thejpster/monotron/avr_kb/src/keycodes.h

/**
 * Keycodes for Scan Code Set 2.
 */

#define KEYCODE_SCS2_F9 0x01
#define KEYCODE_SCS2_F5 0x03
#define KEYCODE_SCS2_F3 0x04
#define KEYCODE_SCS2_F1 0x05
#define KEYCODE_SCS2_F2 0x06
#define KEYCODE_SCS2_F12 0x07
#define KEYCODE_SCS2_F10 0x09
#define KEYCODE_SCS2_F8 0x0A
#define KEYCODE_SCS2_F6 0x0B
#define KEYCODE_SCS2_F4 0x0C
#define KEYCODE_SCS2_TAB 0x0D
#define KEYCODE_SCS2_BACKTICK 0x0E
#define KEYCODE_SCS2_ALTLEFT 0x11
#define KEYCODE_SCS2_SHIFTLEFT 0x12
#define KEYCODE_SCS2_CONTROLLEFT 0x14
#define KEYCODE_SCS2_Q 0x15
#define KEYCODE_SCS2_KEY1 0x16
#define KEYCODE_SCS2_Z 0x1A
#define KEYCODE_SCS2_S 0x1B
#define KEYCODE_SCS2_A 0x1C
#define KEYCODE_SCS2_W 0x1D
#define KEYCODE_SCS2_KEY2 0x1e
#define KEYCODE_SCS2_C 0x21
#define KEYCODE_SCS2_X 0x22
#define KEYCODE_SCS2_D 0x23
#define KEYCODE_SCS2_E 0x24
#define KEYCODE_SCS2_KEY4 0x25
#define KEYCODE_SCS2_KEY3 0x26
#define KEYCODE_SCS2_SPACEBAR 0x29
#define KEYCODE_SCS2_V 0x2A
#define KEYCODE_SCS2_F 0x2B
#define KEYCODE_SCS2_T 0x2C
#define KEYCODE_SCS2_R 0x2D
#define KEYCODE_SCS2_KEY5 0x2E
#define KEYCODE_SCS2_N 0x31
#define KEYCODE_SCS2_B 0x32
#define KEYCODE_SCS2_H 0x33
#define KEYCODE_SCS2_G 0x34
#define KEYCODE_SCS2_Y 0x35
#define KEYCODE_SCS2_KEY6 0x36
#define KEYCODE_SCS2_M 0x3A
#define KEYCODE_SCS2_J 0x3B
#define KEYCODE_SCS2_U 0x3C
#define KEYCODE_SCS2_KEY7 0x3D
#define KEYCODE_SCS2_KEY8 0x3E
#define KEYCODE_SCS2_COMMA 0x41
#define KEYCODE_SCS2_K 0x42
#define KEYCODE_SCS2_I 0x43
#define KEYCODE_SCS2_O 0x44
#define KEYCODE_SCS2_KEY0 0x45
#define KEYCODE_SCS2_KEY9 0x46
#define KEYCODE_SCS2_FULLSTOP 0x49
#define KEYCODE_SCS2_SLASH 0x4A
#define KEYCODE_SCS2_L 0x4B
#define KEYCODE_SCS2_SEMICOLON 0x4C
#define KEYCODE_SCS2_P 0x4D
#define KEYCODE_SCS2_MINUS 0x4E
#define KEYCODE_SCS2_QUOTE 0x52
#define KEYCODE_SCS2_BRACKETSQUARELEFT 0x54
#define KEYCODE_SCS2_EQUALS 0x55
#define KEYCODE_SCS2_CAPSLOCK 0x58
#define KEYCODE_SCS2_SHIFTRIGHT 0x59
#define KEYCODE_SCS2_ENTER 0x5A
#define KEYCODE_SCS2_BRACKETSQUARERIGHT 0x5B
#define KEYCODE_SCS2_BACKSLASH 0x5D
#define KEYCODE_SCS2_BACKSPACE 0x66
#define KEYCODE_SCS2_NUMPAD1 0x69
#define KEYCODE_SCS2_NUMPAD4 0x6B
#define KEYCODE_SCS2_NUMPAD7 0x6C
#define KEYCODE_SCS2_NUMPAD0 0x70
#define KEYCODE_SCS2_NUMPADPERIOD 0x71
#define KEYCODE_SCS2_NUMPAD2 0x72
#define KEYCODE_SCS2_NUMPAD5 0x73
#define KEYCODE_SCS2_NUMPAD6 0x74
#define KEYCODE_SCS2_NUMPAD8 0x75
#define KEYCODE_SCS2_ESCAPE 0x76
#define KEYCODE_SCS2_NUMPADLOCK 0x77
#define KEYCODE_SCS2_F11 0x78
#define KEYCODE_SCS2_NUMPADPLUS 0x79
#define KEYCODE_SCS2_NUMPAD3 0x7A
#define KEYCODE_SCS2_NUMPADMINUS 0x7B
#define KEYCODE_SCS2_NUMPADSTAR 0x7C
#define KEYCODE_SCS2_NUMPAD9 0x7D
#define KEYCODE_SCS2_SCROLLLOCK 0x7E
#define KEYCODE_SCS2_F7 0x83

#define KEYCODE_SCS2_EXTENDED_ALTRIGHT 0x11
#define KEYCODE_SCS2_EXTENDED_CONTROLRIGHT 0x14
#define KEYCODE_SCS2_EXTENDED_WINDOWSLEFT 0x1F
#define KEYCODE_SCS2_EXTENDED_WINDOWSRIGHT 0x27
#define KEYCODE_SCS2_EXTENDED_MENUS 0x2F
#define KEYCODE_SCS2_EXTENDED_NUMPADSLASH 0x4A
#define KEYCODE_SCS2_EXTENDED_NUMPADENTER 0x5A
#define KEYCODE_SCS2_EXTENDED_END 0x69
#define KEYCODE_SCS2_EXTENDED_ARROWLEFT 0x6B
#define KEYCODE_SCS2_EXTENDED_HOME 0x6C
#define KEYCODE_SCS2_EXTENDED_INSERT 0x70
#define KEYCODE_SCS2_EXTENDED_DELETE 0x71
#define KEYCODE_SCS2_EXTENDED_ARROWDOWN 0x72
#define KEYCODE_SCS2_EXTENDED_ARROWRIGHT 0x74
#define KEYCODE_SCS2_EXTENDED_ARROWUP 0x75
#define KEYCODE_SCS2_EXTENDED_PAGEDOWN 0x7A
#define KEYCODE_SCS2_EXTENDED_PAGEUP 0x7D
