thejpster/monotron/src/ui/mod.rs

use super::{Context, Input, APPLICATION_RAM, FRAMEBUFFER};
use asm;
use core::fmt::Write;
use embedded_hal::prelude::*;
use fb;
use fb::{BaseConsole, AsciiConsole};
use menu;

mod rust_logo;

pub(crate) type Menu<'a> = menu::Menu<'a, Context>;
pub(crate) type Item<'a> = menu::Item<'a, Context>;

const TEST_ALPHABET: Item = Item {
    item_type: menu::ItemType::Callback(test_alphabet),
    command: "alphabet",
    help: Some("Scrolls some test text output."),
};

const TEST_CLEAR: Item = Item {
    item_type: menu::ItemType::Callback(test_clear),
    command: "clear",
    help: Some("Resets the display."),
};

const TEST_ANIMATION: Item = Item {
    item_type: menu::ItemType::Callback(test_animation),
    command: "animate",
    help: Some("Bounces argument around."),
};

const TEST_ART: Item = Item {
    item_type: menu::ItemType::Callback(test_art),
    command: "art",
    help: Some("Show some art."),
};

const ITEM_PEEK: Item = Item {
    item_type: menu::ItemType::Callback(item_peek),
    command: "peek",
    help: Some("<addr> - Read a register."),
};

const ITEM_POKE: Item = Item {
    item_type: menu::ItemType::Callback(item_poke),
    command: "poke",
    help: Some("<addr> <value> - Write a register."),
};

const ITEM_DUMP: Item = Item {
    item_type: menu::ItemType::Callback(item_dump),
    command: "dump",
    help: Some("<addr> <bytes> - Dump RAM/ROM."),
};

const ITEM_LOAD: Item = Item {
    item_type: menu::ItemType::Callback(load_file),
    command: "load",
    help: Some("<len> - Load program from UART."),
};

const ITEM_DEBUG: Item = Item {
    item_type: menu::ItemType::Callback(debug_info),
    command: "debug",
    help: Some("- Show some debug info."),
};

const ITEM_RUN: Item = Item {
    item_type: menu::ItemType::Callback(run_program),
    command: "run",
    help: Some("Run loaded program."),
};

pub(crate) const ROOT_MENU: Menu = Menu {
    label: "root",
    items: &[
        &TEST_ALPHABET,
        &TEST_ANIMATION,
        &TEST_ART,
        &TEST_CLEAR,
        &ITEM_PEEK,
        &ITEM_POKE,
        &ITEM_DUMP,
        &ITEM_LOAD,
        &ITEM_RUN,
        &ITEM_DEBUG,
    ],
    entry: None,
    exit: None,
};

struct Fire {
    seed: u32,
    buffer: [u32; Fire::FLAME_BUFFER_LEN],
}

/// The test menu item - displays all the glyphs in all the colour combinations
fn test_alphabet<'a>(_menu: &Menu, _item: &Item, _input: &str, context: &mut Context) {
    let mut old_frame = 0;
    let mut ch = 0u8;
    const COLOURS: [fb::Colour; 8] = [
        fb::Colour::Blue,
        fb::Colour::Black,
        fb::Colour::Red,
        fb::Colour::Magenta,
        fb::Colour::Green,
        fb::Colour::Yellow,
        fb::Colour::Cyan,
        fb::Colour::White,
    ];
    let mut fg_wheel = COLOURS.iter().cycle();
    let mut bg_wheel = COLOURS.iter().cycle();
    let mut fg = fg_wheel.next();
    let mut bg = bg_wheel.next();
    loop {
        asm::wfi();
        let new_frame = unsafe { FRAMEBUFFER.frame() };
        if new_frame != old_frame {
            old_frame = new_frame;
            unsafe {
                FRAMEBUFFER.write_glyph(
                    fb::Char::from_byte(ch),
                    Some(fb::Attr::new(*fg.unwrap(), *bg.unwrap())),
                );
            }
            fg = fg_wheel.next();
            if ch == 255 {
                bg = bg_wheel.next();
                ch = 0;
            } else {
                ch += 1;
            }
        }
        if let Some(_input) = context.read() {
            break;
        }
    }
}

/// Clears the screen
fn test_clear<'a>(_menu: &Menu, _item: &Item, _input: &str, _context: &mut Context) {
    unsafe { FRAMEBUFFER.clear() };
    unsafe { FRAMEBUFFER.set_pos(fb::Position::origin()).unwrap() };
}

/// Display some art
fn test_art<'a>(_menu: &Menu, _item: &Item, _input: &str, context: &mut Context) {
    unsafe {
        FRAMEBUFFER.clear();
    }
    write!(context, "SCORE 0300      HIGH 0000          3    ╩       ").unwrap();
    write!(context, "  ▀▄ ▄▀     ▀▄ ▄▀     ▀▄ ▄▀     ▀▄ ▄▀           ").unwrap();
    write!(context, " ▄█▀█▀█▄   ▄█▀█▀█▄   ▄█▀█▀█▄   ▄█▀█▀█▄          ").unwrap();
    write!(context, "█▀█████▀█ █▀█████▀█ █▀█████▀█ █▀█████▀█         ").unwrap();
    write!(context, "▀ ▀▄ ▄▀ ▀ ▀ ▀▄ ▄▀ ▀ ▀ ▀▄ ▄▀ ▀ ▀ ▀▄ ▄▀ ▀         ").unwrap();
    writeln!(context, "").unwrap();
    write!(context, "  ▀▄ ▄▀     ▀▄ ▄▀     ▀▄ ▄▀     ▀▄ ▄▀           ").unwrap();
    write!(context, " ▄█▀█▀█▄   ▄█▀█▀█▄   ▄█▀█▀█▄   ▄█▀█▀█▄          ").unwrap();
    write!(context, "█▀█████▀█ █▀█████▀█ █▀█████▀█ █▀█████▀█         ").unwrap();
    write!(context, "▀ ▀▄ ▄▀ ▀ ▀ ▀▄ ▄▀ ▀ ▀ ▀▄ ▄▀ ▀ ▀ ▀▄ ▄▀ ▀         ").unwrap();
    writeln!(context, "").unwrap();
    write!(context, "  ▀▄ ▄▀     ▀▄ ▄▀     ▀▄ ▄▀     ▀▄ ▄▀           ").unwrap();
    write!(context, " ▄█▀█▀█▄   ▄█▀█▀█▄   ▄█▀█▀█▄   ▄█▀█▀█▄          ").unwrap();
    write!(context, "█▀█████▀█ █▀█████▀█ █▀█████▀█ █▀█████▀█         ").unwrap();
    write!(context, "▀ ▀▄ ▄▀ ▀ ▀ ▀▄ ▄▀ ▀ ▀ ▀▄ ▄▀ ▀ ▀ ▀▄ ▄▀ ▀         ").unwrap();
    writeln!(context, "").unwrap();
    writeln!(context, "        |").unwrap();
    write!(context, "  ██░▒  |   ████      ████      ████      ████  ").unwrap();
    write!(context, "██████▓▓  ████████  ████████  ████████  ████████").unwrap();
    writeln!(context, "").unwrap();
    writeln!(context, "       ═╩═").unwrap();
    writeln!(context, "Press a key...").unwrap();
    loop {
        asm::wfi();
        if let Some(_input) = context.read() {
            break;
        }
    }
    writeln!(context, "\u{001b}Y\u{001b}k\u{001b}Z").unwrap();
    writeln!(context, "              1UP   HIGH SCORE").unwrap();
    writeln!(context, "                00        00").unwrap();
    writeln!(context, "\u{001b}G          ╔════════════╦╦════════════╗").unwrap();
    writeln!(context, "          ║\u{001b}C············\u{001b}G║║\u{001b}C············\u{001b}G║").unwrap();
    writeln!(context, "          ║\u{001b}C·\u{001b}G┌──┐\u{001b}C·\u{001b}G┌───┐\u{001b}C·\u{001b}G║║\u{001b}C·\u{001b}G┌───┐\u{001b}C·\u{001b}G┌──┐\u{001b}C·\u{001b}G║").unwrap();
    writeln!(context, "          ║○│  │\u{001b}C·\u{001b}G│   │\u{001b}C·\u{001b}G║║\u{001b}C·\u{001b}G│   │\u{001b}C·\u{001b}G│  │○║").unwrap();
    writeln!(context, "          ║\u{001b}C·\u{001b}G└──┘\u{001b}C·\u{001b}G└───┘\u{001b}C·\u{001b}G╚╝\u{001b}C·\u{001b}G└───┘\u{001b}C·\u{001b}G└──┘\u{001b}C·\u{001b}G║").unwrap();
    writeln!(context, "          ║\u{001b}C··························\u{001b}G║").unwrap();
    writeln!(context, "          ║\u{001b}C·\u{001b}G┌──┐\u{001b}C·\u{001b}G┌┐\u{001b}C·\u{001b}G┌──────┐\u{001b}C·\u{001b}G┌┐\u{001b}C·\u{001b}G┌──┐\u{001b}C·\u{001b}G║").unwrap();
    writeln!(context, "          ║\u{001b}C·\u{001b}G└──┘\u{001b}C·\u{001b}G││\u{001b}C·\u{001b}G└──┐┌──┘\u{001b}C·\u{001b}G││\u{001b}C·\u{001b}G└──┘\u{001b}C·\u{001b}G║").unwrap();
    writeln!(context, "          ║\u{001b}C······\u{001b}G││\u{001b}C····\u{001b}G││\u{001b}C····\u{001b}G││\u{001b}C······\u{001b}G║").unwrap();
    writeln!(context, "          ╚════╗\u{001b}C·\u{001b}G│└──┐ ││ ┌──┘│\u{001b}C·\u{001b}G╔════╝").unwrap();
    writeln!(context, "               ║\u{001b}C·\u{001b}G│┌──┘ └┘ └──┐│\u{001b}C·\u{001b}G║     ").unwrap();
    writeln!(context, "               ║\u{001b}C·\u{001b}G││    \u{001b}Y☺\u{001b}G     ││\u{001b}C·\u{001b}G║     ").unwrap();
    writeln!(context, "          ═════╝\u{001b}C·\u{001b}G└┘ ╔══════╗ └┘\u{001b}C·\u{001b}G╚═════").unwrap();
    writeln!(context, "                \u{001b}C·\u{001b}G   ║\u{001b}R☺ \u{001b}G☺ \u{001b}B☺\u{001b}G ║   \u{001b}C·\u{001b}G      ").unwrap();
    writeln!(context, "          ═════╗\u{001b}C·\u{001b}G┌┐ ╚══════╝ ┌┐\u{001b}C·\u{001b}G╔═════").unwrap();
    writeln!(context, "               ║\u{001b}C·\u{001b}G││  READY!  ││\u{001b}C·\u{001b}G║     ").unwrap();
    writeln!(context, "               ║\u{001b}C·\u{001b}G││ ┌──────┐ ││\u{001b}C·\u{001b}G║     ").unwrap();
    writeln!(context, "          ╔════╝\u{001b}C·\u{001b}G└┘ └──┐┌──┘ └┘\u{001b}C·\u{001b}G╚════╗").unwrap();
    writeln!(context, "          ║\u{001b}C············\u{001b}G││\u{001b}C············\u{001b}G║").unwrap();
    writeln!(context, "          ║\u{001b}C·\u{001b}G┌──┐\u{001b}C·\u{001b}G┌───┐\u{001b}C·\u{001b}G││\u{001b}C·\u{001b}G┌───┐\u{001b}C·\u{001b}G┌──┐\u{001b}C·\u{001b}G║").unwrap();
    writeln!(context, "          ║\u{001b}C·\u{001b}G└─┐│\u{001b}C·\u{001b}G└───┘\u{001b}C·\u{001b}G└┘\u{001b}C·\u{001b}G└───┘\u{001b}C·\u{001b}G│┌─┘\u{001b}C·\u{001b}G║").unwrap();
    writeln!(context, "          ║○\u{001b}C··\u{001b}G││\u{001b}C·······\u{001b}Y◄►\u{001b}C·······\u{001b}G││\u{001b}C··\u{001b}G○║").unwrap();
    writeln!(context, "          ╠═╗\u{001b}C·\u{001b}G││\u{001b}C·\u{001b}G┌┐\u{001b}C·\u{001b}G┌──────┐\u{001b}C·\u{001b}G┌┐\u{001b}C·\u{001b}G││\u{001b}C·\u{001b}G╔═╣").unwrap();
    writeln!(context, "          ╠═╝\u{001b}C·\u{001b}G└┘\u{001b}C·\u{001b}G││\u{001b}C·\u{001b}G└──┐┌──┘\u{001b}C·\u{001b}G││\u{001b}C·\u{001b}G└┘\u{001b}C·\u{001b}G╚═╣").unwrap();
    writeln!(context, "          ║\u{001b}C······\u{001b}G││\u{001b}C····\u{001b}G││\u{001b}C····\u{001b}G││\u{001b}C······\u{001b}G║").unwrap();
    writeln!(context, "          ║\u{001b}C·\u{001b}G┌────┘└──┐\u{001b}C·\u{001b}G││\u{001b}C·\u{001b}G┌──┘└────┐\u{001b}C·\u{001b}G║").unwrap();
    writeln!(context, "          ║\u{001b}C·\u{001b}G└────────┘\u{001b}C·\u{001b}G└┘\u{001b}C·\u{001b}G└────────┘\u{001b}C·\u{001b}G║").unwrap();
    writeln!(context, "          ║\u{001b}C··························\u{001b}G║").unwrap();
    writeln!(context, "          ╚══════════════════════════╝").unwrap();
    writeln!(context, "             ◄► ◄► ◄►").unwrap();
    write!(context, "\n\n\nPress a key...").unwrap();
    loop {
        asm::wfi();
        if let Some(_input) = context.read() {
            break;
        }
    }

    write!(context, "\u{001b}Z\u{001b}K\u{001b}w  \u{001b}RF\u{001b}Kile   \u{001b}RE\u{001b}Kdit  \u{001b}RV\u{001b}Kiew   \u{001b}RT\u{001b}Kools  \u{001b}RH\u{001b}Kelp               ").unwrap();
    write!(context, "\u{001b}B\u{001b}c████████████████████████████████████████████████").unwrap();
    write!(context, "████████████████████████████████████████████████").unwrap();
    write!(context, "████████████████████████████████████████████████").unwrap();
    write!(context, "████████████████████████████████████████████████").unwrap();
    write!(context, "████████████████████████████████████████████████").unwrap();
    write!(context, "████████████████████████████████████████████████").unwrap();
    write!(context, "████████████████████████████████████████████████").unwrap();
    write!(context, "████████████████████████████\u{001b}W\u{001b}b┌[Calc]──X┐    \u{001b}B\u{001b}c█████").unwrap();
    write!(context, "████████████████████████████\u{001b}W\u{001b}b│\u{001b}B\u{001b}k         \u{001b}W\u{001b}b│\u{001b}B\u{001b}k▒\u{001b}c██\u{001b}W\u{001b}b \u{001b}B\u{001b}c█████").unwrap();
    write!(context, "███\u{001b}W\u{001b}m┌[Calendar]───────────X┐\u{001b}B\u{001b}c█\u{001b}W\u{001b}b│\u{001b}B\u{001b}k         \u{001b}W\u{001b}b│\u{001b}B\u{001b}k▒\u{001b}c██\u{001b}W\u{001b}b \u{001b}B\u{001b}c█████").unwrap();
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
    write!(context, "███\u{001b}W\u{001b}m└──────────────────────┘\u{001b}B\u{001b}k▒\u{001b}c████████████████████").unwrap();
    write!(context, "████\u{001b}k▒▒▒▒▒▒▒▒▒▒▒▒▒▒▒▒▒▒▒▒▒▒▒▒\u{001b}c████████████████████").unwrap();
    write!(context, "████████████████████████████████████████████████").unwrap();
    write!(context, "████████████████████████████████████████████████").unwrap();
    write!(context, "████████████████████████████████████████████████").unwrap();
    write!(context, "████████████████████████████████████████████████").unwrap();
    write!(context, "████████████████████████████████████████████████").unwrap();
    write!(context, "████████████████████████████████████████████████").unwrap();
    write!(context, "\u{001b}K\u{001b}w▒\u{001b}W\u{001b}kCAPS\u{001b}K\u{001b}w▒\u{001b}W\u{001b}kINS\u{001b}K\u{001b}w▒▒▒▒▒▒▒▒▒▒▒▒▒▒▒▒▒▒▒▒▒▒▒▒\u{001b}W\u{001b}k[Version v1.2]\u{001b}K\u{001b}w").unwrap();

    loop {
        asm::wfi();
        if let Some(_input) = context.read() {
            writeln!(context, "\u{001b}W\u{001b}b\u{001b}ZOk...").unwrap();
            break;
        }
    }

    write!(context, "\u{001b}Z\u{001b}Y\u{001b}k╔════════════════════════\u{001b}W[MonotronPaint]\u{001b}Y═══════╗").unwrap();
    write!(context, "║\u{001b}W┌[Font]──────────┐┌──────────────────────────┐\u{001b}Y║").unwrap();
    write!(context, "║\u{001b}W│ ☺☻♥♦♣♠•◘○◙♂♀♪♫☼││\u{001b}Y\u{001b}b                          \u{001b}W\u{001b}k│\u{001b}Y║").unwrap();
    write!(context, "║\u{001b}W│►◄↕‼¶§▬↨↑↓→←∟↔▲▼││\u{001b}Y\u{001b}b                          \u{001b}W\u{001b}k│\u{001b}Y║").unwrap();
    write!(context, "║\u{001b}W│ !\"#$%&'()*+,-./││\u{001b}Y\u{001b}b                          \u{001b}W\u{001b}k│\u{001b}Y║").unwrap();
    write!(context, "║\u{001b}W│0123456789:;<=>?││\u{001b}Y\u{001b}b                          \u{001b}W\u{001b}k│\u{001b}Y║").unwrap();
    write!(context, "║\u{001b}W│@ABCDEFGHIJKLMNO││\u{001b}Y\u{001b}b                          \u{001b}W\u{001b}k│\u{001b}Y║").unwrap();
    write!(context, "║\u{001b}W│PQRSTUVWXYZ[\\]^_││\u{001b}Y\u{001b}b          ▓▓▓▓▓▓▓         \u{001b}W\u{001b}k│\u{001b}Y║").unwrap();
    write!(context, "║\u{001b}W│`abcdefghijklmno││\u{001b}Y\u{001b}b        ▓▓▓▓▓▓▓▓▓▓▓       \u{001b}W\u{001b}k│\u{001b}Y║").unwrap();
    write!(context, "║\u{001b}W│pqrstuvwxyz{{|}}~ ││\u{001b}Y\u{001b}b       ▓▓▓▓▓▓▓▓▓▓▓▓▓      \u{001b}W\u{001b}k│\u{001b}Y║").unwrap();
    write!(context, "║\u{001b}W│ÇüéâäàåçêëèïîìÄÅ││\u{001b}Y\u{001b}b     ▓▓▓▓▓▓▓▓▓▓▓▓▓▓▓▓▓    \u{001b}W\u{001b}k│\u{001b}Y║").unwrap();
    write!(context, "║\u{001b}W│ÉæÆôöòûùÿÖÜø£Ø×ƒ││\u{001b}Y\u{001b}b     ▓▓▓▓▓▓▓▓▓▓▓▓▓▓▓▓▓    \u{001b}W\u{001b}k│\u{001b}Y║").unwrap();
    write!(context, "║\u{001b}W│áíóúñÑªº¿®¬½¼¡«»││\u{001b}Y\u{001b}b    ▓▓▓\u{001b}K\u{001b}k▓▓▓\u{001b}Y\u{001b}b▓▓▓▓▓▓\u{001b}K\u{001b}k▓▓▓\u{001b}Y\u{001b}b▓▓▓▓   \u{001b}W\u{001b}k│\u{001b}Y║").unwrap();
    write!(context, "║\u{001b}W│░▒▓│┤ÁÂÀ©╣║╗╝¢¥┐││\u{001b}Y\u{001b}b   ▓▓▓\u{001b}K\u{001b}k▓▓▓▓▓\u{001b}Y\u{001b}b▓▓▓▓\u{001b}K\u{001b}k▓▓▓▓▓\u{001b}Y\u{001b}b▓▓▓▓  \u{001b}W\u{001b}k│\u{001b}Y║").unwrap();
    write!(context, "║\u{001b}W│└┴┬├─┼ãÃ╚╔╩╦╠═╬¤││\u{001b}Y\u{001b}b   ▓▓▓\u{001b}K\u{001b}k▓▓▓▓▓\u{001b}Y\u{001b}b▓▓▓▓\u{001b}K\u{001b}k▓▓▓▓▓\u{001b}Y\u{001b}b▓▓▓▓  \u{001b}W\u{001b}k│\u{001b}Y║").unwrap();
    write!(context, "║\u{001b}W│ðÐÊËÈıÍÎÏ┘┌█▄¦Ì▀││\u{001b}Y\u{001b}b  ▓▓▓▓\u{001b}K\u{001b}k▓▓▓▓▓\u{001b}Y\u{001b}b▓▓▓▓\u{001b}K\u{001b}k▓▓▓▓▓\u{001b}Y\u{001b}b▓▓▓▓▓ \u{001b}W\u{001b}k│\u{001b}Y║").unwrap();
    write!(context, "║\u{001b}W│ÓßÔÒõÕµþÞÚÛÙýÝ¯´││\u{001b}Y\u{001b}b  ▓▓▓▓▓\u{001b}K\u{001b}k▓▓▓\u{001b}Y\u{001b}b▓▓▓▓▓▓\u{001b}K\u{001b}k▓▓▓\u{001b}Y\u{001b}b▓▓▓▓▓▓ \u{001b}W\u{001b}k│\u{001b}Y║").unwrap();
    write!(context, "║\u{001b}W│-±‗¾¶§÷¸°¨·¹³²■\u{00a0}││\u{001b}Y\u{001b}b  ▓▓▓▓▓▓▓▓▓▓▓▓▓▓▓▓▓▓▓▓▓▓▓ \u{001b}W\u{001b}k│\u{001b}Y║").unwrap();
    write!(context, "║\u{001b}W└────────────────┘│\u{001b}Y\u{001b}b  ▓▓▓▓▓▓▓▓▓▓▓▓▓▓▓▓▓▓▓▓▓▓▓ \u{001b}W\u{001b}k│\u{001b}Y║").unwrap();
    write!(context, "║\u{001b}W┌[Colour]┐┌[Menu]┐│\u{001b}Y\u{001b}b  ▓▓▓▓▓▓▓▓▓▓▓▓▓▓▓▓▓▓▓▓▓▓▓ \u{001b}W\u{001b}k│\u{001b}Y║").unwrap();
    write!(context, "║\u{001b}W│\u{001b}R█\u{001b}G█\u{001b}B█\u{001b}Y█\u{001b}M█\u{001b}C█\u{001b}K█\u{001b}W█││L\u{001b}Mo\u{001b}Wad\u{001b}K  \u{001b}W││\u{001b}Y\u{001b}b  ▓▓▓▓▓\u{001b}K\u{001b}k▓\u{001b}Y\u{001b}b▓▓▓▓▓▓▓▓▓▓▓▓\u{001b}K\u{001b}k▓\u{001b}Y\u{001b}b▓▓▓▓ \u{001b}W\u{001b}k│\u{001b}Y║").unwrap();
    write!(context, "║\u{001b}W└────────┘│\u{001b}MS\u{001b}Wave\u{001b}K  \u{001b}W││\u{001b}Y\u{001b}b  ▓▓▓▓▓\u{001b}K\u{001b}k▓▓\u{001b}Y\u{001b}b▓▓▓▓▓▓▓▓▓▓\u{001b}K\u{001b}k▓▓\u{001b}Y\u{001b}b▓▓▓▓ \u{001b}W\u{001b}k│\u{001b}Y║").unwrap();
    write!(context, "║\u{001b}W┌[Tools]─┐│\u{001b}MP\u{001b}Wrint\u{001b}K \u{001b}W││\u{001b}Y\u{001b}b   ▓▓▓▓▓\u{001b}K\u{001b}k▓▓\u{001b}Y\u{001b}b▓▓▓▓▓▓▓▓▓\u{001b}K\u{001b}k▓\u{001b}Y\u{001b}b▓▓▓▓  \u{001b}W\u{001b}k│\u{001b}Y║").unwrap();
    write!(context, "║\u{001b}W│\u{001b}MR\u{001b}Wect\u{001b}K    \u{001b}W││\u{001b}ME\u{001b}Wxport││\u{001b}Y\u{001b}b   ▓▓▓▓▓▓\u{001b}K\u{001b}k▓\u{001b}Y\u{001b}b▓▓▓▓▓▓▓\u{001b}K\u{001b}k▓▓▓\u{001b}Y\u{001b}b▓▓▓▓  \u{001b}W\u{001b}k│\u{001b}Y║").unwrap();
    write!(context, "║\u{001b}W│\u{001b}MC\u{001b}Well\u{001b}K    \u{001b}W││C\u{001b}Ml\u{001b}Wear\u{001b}K \u{001b}W││\u{001b}Y\u{001b}b    ▓▓▓▓▓▓\u{001b}K\u{001b}k▓▓▓▓▓▓▓▓\u{001b}Y\u{001b}b▓▓▓▓▓   \u{001b}W\u{001b}k│\u{001b}Y║").unwrap();
    write!(context, "║\u{001b}W│\u{001b}ML\u{001b}Wine\u{001b}K    \u{001b}W││\u{001b}K      \u{001b}W││\u{001b}Y\u{001b}b     ▓▓▓▓▓▓▓▓▓▓▓▓▓▓▓▓▓    \u{001b}W\u{001b}k│\u{001b}Y║").unwrap();
    write!(context, "║\u{001b}W│\u{001b}MF\u{001b}Will\u{001b}K    \u{001b}W│└──────┘│\u{001b}Y\u{001b}b     ▓▓▓▓▓▓▓▓▓▓▓▓▓▓▓▓▓    \u{001b}W\u{001b}k│\u{001b}Y║").unwrap();
    write!(context, "║\u{001b}W│\u{001b}M\u{001b}cT\u{001b}Kext    \u{001b}W\u{001b}k│┌[Layr]┐│\u{001b}Y\u{001b}b       ▓▓▓▓▓▓▓▓▓▓▓▓▓      \u{001b}W\u{001b}k│\u{001b}Y║").unwrap();
    write!(context, "║\u{001b}W│\u{001b}MC\u{001b}Wopy\u{001b}K    \u{001b}W││\u{001b}K      \u{001b}W││\u{001b}Y\u{001b}b        ▓▓▓▓▓▓▓▓▓▓▓       \u{001b}W\u{001b}k│\u{001b}Y║").unwrap();
    write!(context, "║\u{001b}W│\u{001b}MP\u{001b}Waste\u{001b}K   \u{001b}W││1  \u{001b}GH\u{001b}RL\u{001b}WX││\u{001b}Y\u{001b}b          ▓▓▓▓▓▓▓         \u{001b}W\u{001b}k│\u{001b}Y║").unwrap();
    write!(context, "║\u{001b}W└────────┘│2  \u{001b}GH\u{001b}RL\u{001b}WX││\u{001b}Y\u{001b}b                          \u{001b}W\u{001b}k│\u{001b}Y║").unwrap();
    write!(context, "║\u{001b}W┌[Info]──┐│3  \u{001b}RH\u{001b}GL\u{001b}WX││\u{001b}Y\u{001b}b                          \u{001b}W\u{001b}k│\u{001b}Y║").unwrap();
    write!(context, "║\u{001b}W│N:Test\u{001b}K  \u{001b}W││4  \u{001b}GHL\u{001b}WX││\u{001b}Y\u{001b}b                          \u{001b}W\u{001b}k│\u{001b}Y║").unwrap();
    write!(context, "║\u{001b}W│S:48x36 ││\u{001b}K      \u{001b}W││\u{001b}Y\u{001b}b                          \u{001b}W\u{001b}k│\u{001b}Y║").unwrap();
    write!(context, "║\u{001b}W└────────┘└──────┘└──────────────────────────┘\u{001b}Y║").unwrap();
    write!(context, "╚══════════════════════════════════════════════").unwrap();

    loop {
        asm::wfi();
        if let Some(_input) = context.read() {
            break;
        }
    }

    let mode2_buffer = unsafe { &mut super::APPLICATION_RAM[0..384 * 288 / 8] };

    unsafe {
        FRAMEBUFFER.clear();
    }

    for (src, dest) in rust_logo::RUST_LOGO_DATA
        .iter()
        .zip(mode2_buffer.iter_mut())
    {
        // Our source is an X-Bitmap, which puts the pixels in LSB-first order.
        // We need MSB first order for Monotron.
        *dest = flip_byte(*src);
    }

    // Attach a graphical buffer at a scan-line. It is interpreted as
    // being a grid 48 bytes wide and as long as given. Each line
    // is output twice. We've attached it to the first scan-line.
    unsafe {
        FRAMEBUFFER.mode2(mode2_buffer, 0);
    }
    let mut start = 0;
    let mut up = true;

    let mut next_frame = unsafe { FRAMEBUFFER.frame() } + 1;
    loop {
        asm::wfi();
        let this_frame = unsafe { FRAMEBUFFER.frame() };
        if this_frame == next_frame {
            if up {
                start += 1;
                if start == 288 {
                    up = false;
                }
            } else {
                start -= 1;
                if start == 0 {
                    up = true;
                }
            }
            unsafe {
                FRAMEBUFFER.mode2_shift(start);
            }
            next_frame = this_frame + 1;
        }
        if let Some(_input) = context.read() {
            break;
        }
    }

    unsafe {
        FRAMEBUFFER.mode2_release();
    }

    write!(context, "\u{001b}Z\u{001b}W\u{001b}k╔══════════════════════════════════════════════╗").unwrap();
    write!(context, "║\u{001b}R█████\u{001b}K \u{001b}R\u{001b}y█████\u{001b}K\u{001b}k \u{001b}Y██  █\u{001b}K \u{001b}G█████\u{001b}K \u{001b}G\u{001b}y█\u{001b}k█\u{001b}y█\u{001b}k██\u{001b}K \u{001b}B████\u{001b}K \u{001b}B█████\u{001b}K \u{001b}M██  █\u{001b}W║").unwrap();
    write!(context, "║\u{001b}R▓\u{001b}K \u{001b}R▓\u{001b}K \u{001b}R▓\u{001b}K \u{001b}R\u{001b}y▓\u{001b}K\u{001b}k   \u{001b}R\u{001b}y▓\u{001b}K\u{001b}k \u{001b}Y▓\u{001b}K \u{001b}Y▓ ▓\u{001b}K \u{001b}G▓\u{001b}K   \u{001b}G▓\u{001b}K \u{001b}G \u{001b}K \u{001b}G\u{001b}y▓\u{001b}K\u{001b}k \u{001b}G \u{001b}K \u{001b}B\u{001b}g▓\u{001b}K\u{001b}k  \u{001b}B\u{001b}g▓\u{001b}K\u{001b}k \u{001b}B▓\u{001b}K   \u{001b}B▓\u{001b}K \u{001b}M▓\u{001b}K \u{001b}M▓ ▓\u{001b}W║").unwrap();
    write!(context, "║\u{001b}R▒\u{001b}K \u{001b}R▒\u{001b}K \u{001b}R▒\u{001b}K \u{001b}R\u{001b}y▒\u{001b}K\u{001b}k   \u{001b}R\u{001b}y▒\u{001b}K\u{001b}k \u{001b}Y▒\u{001b}K  \u{001b}Y▒▒\u{001b}K \u{001b}G▒\u{001b}K   \u{001b}G▒\u{001b}K \u{001b}G \u{001b}K \u{001b}G\u{001b}y▒\u{001b}K\u{001b}k \u{001b}G \u{001b}K \u{001b}B\u{001b}g▒\u{001b}K\u{001b}k \u{001b}B\u{001b}g▒\u{001b}k \u{001b}K \u{001b}B▒\u{001b}K   \u{001b}B▒\u{001b}K \u{001b}M▒\u{001b}K \u{001b}M ▒▒\u{001b}W║").unwrap();
    write!(context, "║\u{001b}R░ ░\u{001b}K \u{001b}R░\u{001b}K \u{001b}R\u{001b}y░░░░░\u{001b}K\u{001b}k \u{001b}Y░   ░\u{001b}K \u{001b}G░░░░░\u{001b}K \u{001b}G  \u{001b}y░\u{001b}k  \u{001b}K \u{001b}B\u{001b}g░\u{001b}k  \u{001b}g░\u{001b}K\u{001b}k \u{001b}B░░░░░\u{001b}K \u{001b}M░   ░\u{001b}W║").unwrap();
    write!(context, "╚══════════════════════════════════════════════╝").unwrap();
    write!(context, "          by theJPster / @therealjpster").unwrap();
    let mut pos = fb::Position::new(fb::Row(6), fb::Col(0));
    let mut next_frame = unsafe { FRAMEBUFFER.frame() } + 1;
    let mut f = Fire::new();
    loop {
        asm::wfi();
        let this_frame = unsafe { FRAMEBUFFER.frame() };
        if this_frame == next_frame {
            next_frame = this_frame + 1;
            f.draw_fire(unsafe { &mut FRAMEBUFFER });
        }
        match unsafe { FRAMEBUFFER.line() } {
            Some(95) => {
                for col in 13..=21 {
                    pos.col = fb::Col(col);
                    unsafe {
                        FRAMEBUFFER
                            .set_attr_at(pos, fb::Attr::new(fb::Colour::Blue, fb::Colour::Black));
                    }
                }
            }
            Some(101) => {
                for col in 13..=21 {
                    pos.col = fb::Col(col);
                    unsafe {
                        FRAMEBUFFER
                            .set_attr_at(pos, fb::Attr::new(fb::Colour::White, fb::Colour::Black));
                    }
                }
            }
            Some(104) => {
                for col in 13..=21 {
                    pos.col = fb::Col(col);
                    unsafe {
                        FRAMEBUFFER
                            .set_attr_at(pos, fb::Attr::new(fb::Colour::Red, fb::Colour::Black));
                    }
                }
            }
            _ => {}
        }
        if let Some(_input) = context.read() {
            writeln!(context, "\u{001b}W\u{001b}k\u{001b}ZOk...").unwrap();
            break;
        }
    }
}

impl Fire {
    const WIDTH: usize = 48;
    const HEIGHT: usize = 20;
    const SIZE: usize = Self::WIDTH * Self::HEIGHT;
    const FLAME_BUFFER_LEN: usize = Self::SIZE + Self::WIDTH + 1;

    fn new() -> Fire {
        Fire {
            seed: 123456789,
            buffer: [0u32; Self::FLAME_BUFFER_LEN],
        }
    }

    /// Draws a flame effect.
    /// Based on https://gist.github.com/msimpson/1096950.
    fn draw_fire(&mut self, fb: &mut fb::FrameBuffer<super::VideoHardware>) {
        use fb::Char;
        const CHARS: [Char; 10] = [
            Char::Space,
            Char::FullStop,
            Char::Colon,
            Char::CircumflexAccent,
            Char::Asterisk,
            Char::LatinSmallLetterX,
            Char::LatinSmallLetterS,
            Char::LatinCapitalLetterS,
            Char::NumberSign,
            Char::DollarSign,
        ];
        // Seed the fire on the last line
        for _i in 0..5 {
            let idx =
                (Self::WIDTH * (Self::HEIGHT - 1)) + self.random_up_to(Self::WIDTH as u32) as usize;
            self.buffer[idx] = 65;
        }
        // Cascade the flames
        for i in 0..Self::SIZE {
            self.buffer[i] = (self.buffer[i]
                + self.buffer[i + 1]
                + self.buffer[i + Self::WIDTH]
                + self.buffer[i + Self::WIDTH + 1]) / 4;
            let colour = if self.buffer[i] > 15 {
                fb::Colour::Blue
            } else if self.buffer[i] > 9 {
                fb::Colour::Red
            } else if self.buffer[i] > 4 {
                fb::Colour::Yellow
            } else {
                fb::Colour::White
            };
            let glyph = if self.buffer[i] > 9 {
                CHARS[9]
            } else {
                CHARS[self.buffer[i] as usize]
            };
            let pos = fb::Position::new(
                fb::Row(((i / Self::WIDTH) as u8) + 16),
                fb::Col((i % Self::WIDTH) as u8),
            );
            fb.write_glyph_at(glyph, pos, Some(fb::Attr::new(colour, fb::Colour::Black)));
        }
    }

    /// Generates a number in the range [0, limit)
    fn random_up_to(&mut self, limit: u32) -> u32 {
        let buckets = ::core::u32::MAX / limit;
        let upper_edge = buckets * limit;
        loop {
            let try = self.random();
            if try < upper_edge {
                return try / buckets;
            }
        }
    }

    /// Generate a random 32-bit number
    fn random(&mut self) -> u32 {
        self.seed = (self.seed.wrapping_mul(1103515245)).wrapping_add(12345);
        self.seed
    }
}

/// Another test menu item - displays an animation.
fn test_animation<'a>(_menu: &Menu, _item: &Item, input: &str, context: &mut Context) {
    let mut old_frame = 0;
    let mut pos = fb::Position::origin();
    let mut left = true;
    let mut down = true;
    let width = unsafe { FRAMEBUFFER.get_width() };
    let height = unsafe { FRAMEBUFFER.get_height() };
    let input = input.trim_left_matches("animate ");
    let num_chars = input.chars().count();
    let attr =
        unsafe { FRAMEBUFFER.set_attr(fb::Attr::new(fb::Colour::Black, fb::Colour::Yellow)) };
    loop {
        asm::wfi();
        let new_frame = unsafe { FRAMEBUFFER.frame() };
        if new_frame != old_frame {
            old_frame = new_frame;
            if left {
                pos.col.incr();
            } else {
                pos.col.decr();
            }
            if down {
                pos.row.incr();
            } else {
                pos.row.decr();
            }
            if pos.col == fb::Col::origin() {
                left = true;
            }
            if pos.col == fb::Col(width.0 - num_chars as u8) {
                left = false;
            }
            if pos.row == fb::Row::origin() {
                down = true;
            }
            if pos.row == height {
                down = false;
            }
            unsafe {
                FRAMEBUFFER.clear();
                FRAMEBUFFER.set_pos(pos).unwrap();
                write!(FRAMEBUFFER, "{}", input).unwrap();
            }
        }
        if let Some(_input) = context.read() {
            unsafe { FRAMEBUFFER.set_attr(attr) };
            break;
        }
    }
}

fn item_peek<'a>(_menu: &Menu, _item: &Item, input: &str, context: &mut Context) {
    let mut parts = input.split_whitespace();
    parts.next();
    if let Some(addr) = parts
        .next()
        .map_or(None, |p| usize::from_str_radix(p, 16).ok())
    {
        unsafe {
            let data = ::core::ptr::read_volatile(addr as *const u32);
            writeln!(context, "Addr 0x{:08x} is 0x{:08x}", addr, data).unwrap();
        }
    } else {
        writeln!(
            context,
            "Bad address {:?}. Enter hex, without the 0x prefix..",
            input
        ).unwrap();
    }
}

fn item_poke<'a>(_menu: &Menu, _item: &Item, input: &str, context: &mut Context) {
    let mut parts = input.split_whitespace();
    parts.next();
    if let Some(addr) = parts
        .next()
        .map_or(None, |p| usize::from_str_radix(p, 16).ok())
    {
        if let Some(value) = parts
            .next()
            .map_or(None, |p| u32::from_str_radix(p, 16).ok())
        {
            writeln!(context, "Poking 0x{:08x} to addr 0x{:08x}...", value, addr).unwrap();
            unsafe {
                ::core::ptr::write_volatile(addr as *mut u32, value);
            }
        } else {
            writeln!(context, "Missing or bad value.").unwrap();
        }
    } else {
        writeln!(context, "Missing or bad address.").unwrap();
    }
}

fn item_dump<'a>(_menu: &Menu, _item: &Item, input: &str, context: &mut Context) {
    let mut parts = input.split_whitespace();
    parts.next();
    if let Some(mut addr) = parts
        .next()
        .map_or(None, |p| usize::from_str_radix(p, 16).ok())
    {
        if let Some(count) = parts
            .next()
            .map_or(None, |p| u32::from_str_radix(p, 16).ok())
        {
            writeln!(
                context,
                "Dumping 0x{:08x} bytes from 0x{:08x}...",
                count, addr
            ).unwrap();
            for i in 0..count {
                let data = unsafe { ::core::ptr::read_volatile(addr as *const u8) };
                write!(context, "{:02x}", data).unwrap();
                if ((i + 1) % 4) == 0 {
                    write!(context, " ").unwrap();
                }
                if ((i + 1) % 16) == 0 {
                    write!(context, "\n").unwrap();
                }
                addr += 1;
            }
            writeln!(context, "\nDone.").unwrap();
        } else {
            writeln!(context, "Missing or bad value.").unwrap();
        }
    } else {
        writeln!(context, "Missing or bad address.").unwrap();
    }
}

/// Reads raw binary from the UART and dumps it into application RAM.
fn load_file<'a>(_menu: &Menu, _item: &Item, _input: &str, context: &mut Context) {
    unsafe {
        for b in APPLICATION_RAM.iter_mut() {
            *b = 0x00;
        }
    }
    writeln!(context, "Reading hex...").unwrap();
    let mut i = 0;
    let max_bytes = unsafe { APPLICATION_RAM.len() };
    while i < max_bytes {
        let ch = loop {
            match context.rx.read() {
                Ok(x) => break x,
                _ => {}
            }
        };
        let mut byte = match ch {
            b'0' => 0x00,
            b'1' => 0x10,
            b'2' => 0x20,
            b'3' => 0x30,
            b'4' => 0x40,
            b'5' => 0x50,
            b'6' => 0x60,
            b'7' => 0x70,
            b'8' => 0x80,
            b'9' => 0x90,
            b'A' => 0xA0,
            b'B' => 0xB0,
            b'C' => 0xC0,
            b'D' => 0xD0,
            b'E' => 0xE0,
            b'F' => 0xF0,
            b'a' => 0xA0,
            b'b' => 0xB0,
            b'c' => 0xC0,
            b'd' => 0xD0,
            b'e' => 0xE0,
            b'f' => 0xF0,
            _ => return,
        };
        let ch = loop {
            match context.rx.read() {
                Ok(x) => break x,
                _ => {}
            }
        };
        byte |= match ch {
            b'0' => 0x00,
            b'1' => 0x01,
            b'2' => 0x02,
            b'3' => 0x03,
            b'4' => 0x04,
            b'5' => 0x05,
            b'6' => 0x06,
            b'7' => 0x07,
            b'8' => 0x08,
            b'9' => 0x09,
            b'A' => 0x0A,
            b'B' => 0x0B,
            b'C' => 0x0C,
            b'D' => 0x0D,
            b'E' => 0x0E,
            b'F' => 0x0F,
            b'a' => 0x0A,
            b'b' => 0x0B,
            b'c' => 0x0C,
            b'd' => 0x0D,
            b'e' => 0x0E,
            b'f' => 0x0F,
            _ => return,
        };
        unsafe {
            APPLICATION_RAM[i] = byte;
        }
        i = i + 1;
    }
}

/// Print some debug info.
fn debug_info<'a>(_menu: &Menu, _item: &Item, _input: &str, context: &mut Context) {
    let fb_addr = unsafe { &FRAMEBUFFER as *const _ } as usize;
    let app_addr = unsafe { &APPLICATION_RAM as *const _ } as usize;
    writeln!(context, "Framebuffer: 0x{:08x}", fb_addr).unwrap();
    writeln!(context, "Application: 0x{:08x}", app_addr).unwrap();
    let temp = context.spi.cr0.read();
    writeln!(context, "SPI CR0: 0x{:08x}", temp.bits()).unwrap();
    let temp = context.spi.cr1.read();
    writeln!(context, "SPI CR1: 0x{:08x}", temp.bits()).unwrap();
    let temp = context.spi.sr.read();
    writeln!(context, "SPI Status: 0x{:08x}", temp.bits()).unwrap();
}

extern "C" fn puts(_raw_ctx: *mut Context, s: *const u8) -> i32 {
    let mut i = 0;
    unsafe {
        while *s.offset(i) != 0 {
            let ch: u8 = *s.offset(i);
            FRAMEBUFFER.write_character(ch).unwrap();
            i += 1;
        }
    }
    0
}

extern "C" fn putchar(_raw_ctx: *mut Context, ch: u8) -> i32 {
    unsafe { FRAMEBUFFER.write_character(ch).unwrap() };
    ch as i32
}

extern "C" fn readc(raw_ctx: *mut Context) -> i32 {
    let ctx = unsafe {
        &mut *raw_ctx
    };
    loop {
        match ctx.read() {
            None => {
                asm::wfi();
            }
            Some(Input::Unicode(_unicode_char)) => {
                // TODO: Handle keyboard input
                asm::wfi();
            }
            Some(Input::Special(_scancode)) => {
                // TODO: Handle keyboard input
                asm::wfi();
            }
            Some(Input::Utf8(ch)) => {
                return ch as i32;
            }
        }
    }
}

extern "C" fn wfvbi(_raw_ctx: *mut Context) {
    let old_frame = unsafe { FRAMEBUFFER.frame() };
    loop {
        asm::wfi();
        let new_frame = unsafe { FRAMEBUFFER.frame() };
        if new_frame != old_frame {
            break;
        }
    }
}

extern "C" fn kbhit(raw_ctx: *mut Context) -> i32 {
    let ctx = unsafe {
        &mut *raw_ctx
    };
    ctx.has_char() as i32
}

/// Runs a program from application RAM, then returns.
fn run_program<'a>(_menu: &Menu, _item: &Item, _input: &str, context: &mut Context) {
    unsafe {
        let addr = ((APPLICATION_RAM[3] as u32) << 24)
            | ((APPLICATION_RAM[2] as u32) << 16)
            | ((APPLICATION_RAM[1] as u32) << 8)
            | ((APPLICATION_RAM[0] as u32) << 0);
        writeln!(context, "Executing from 0x{:08x}", addr).unwrap();

        // struct callbacks_t {
        //     void* p_context;
        //     int32_t(*putchar)(char ch);
        //     int32_t(*puts)(const char*);
        //     int32_t(*readc)(void* p_context);
        //     int32_t(*wfvbi)(void* p_context);
        //     int32_t(*kbhit)(void* p_context);
        // };

        #[repr(C)]
        struct Table {
            context: *mut Context,
            putchar: extern "C" fn(*mut Context, u8) -> i32,
            puts: extern "C" fn(*mut Context, *const u8) -> i32,
            readc: extern "C" fn(*mut Context) -> i32,
            wfvbi: extern "C" fn(*mut Context),
            kbhit: extern "C" fn(*mut Context) -> i32,
        }
        let t = Table {
            context: context as *mut Context,
            putchar,
            puts,
            readc,
            wfvbi,
            kbhit,
        };
        let ptr = addr as *const ();
        let code: extern "C" fn(*const Table) -> u32 = ::core::mem::transmute(ptr);
        let result = code(&t);
        writeln!(context, "Result: {}", result);
    }
}

fn flip_byte(mut b: u8) -> u8 {
    b = (b & 0xF0) >> 4 | (b & 0x0F) << 4;
    b = (b & 0xCC) >> 2 | (b & 0x33) << 2;
    (b & 0xAA) >> 1 | (b & 0x55) << 1
}

// End of file
